Coltonton/Subaru-OpenPilot-Giraffe/Pictures/image0.jpg

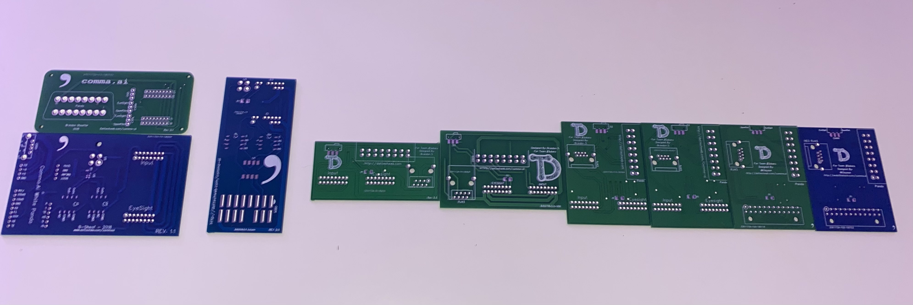
Pictures/image0.jpg
