Coltonton/Subaru-OpenPilot-Giraffe/Pictures/V3/3.1-Viki(1).JPG

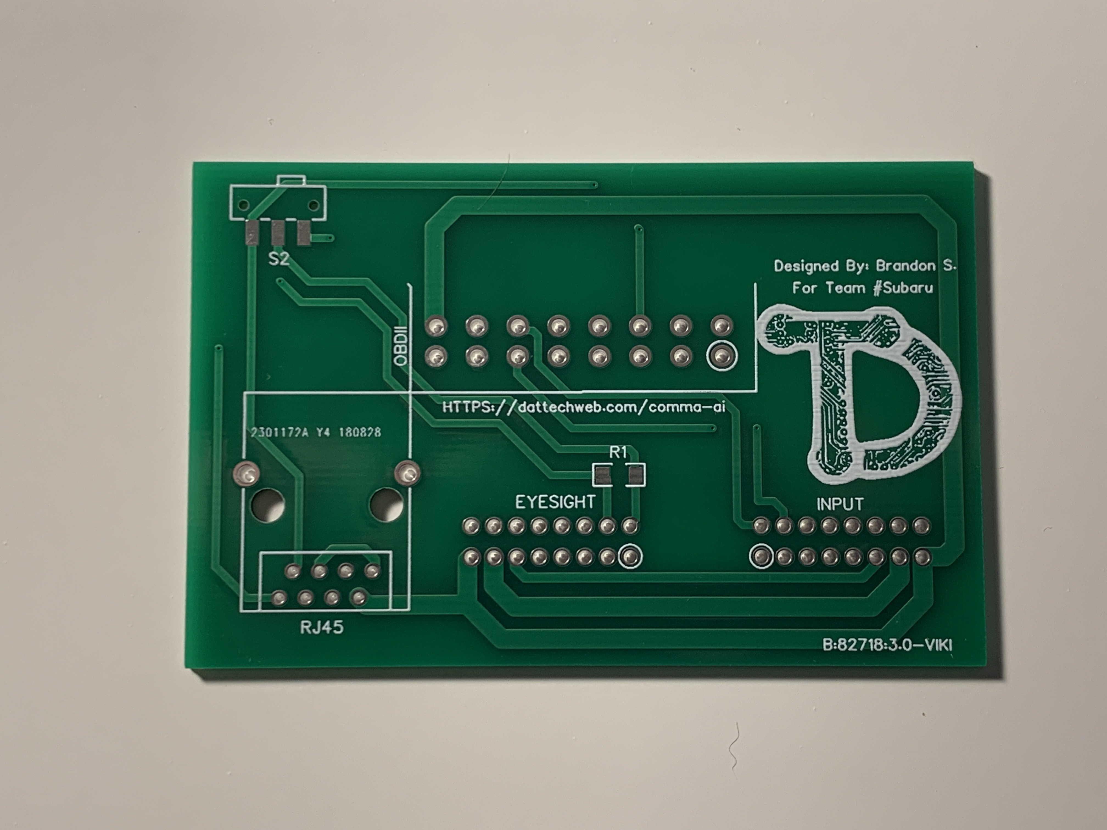
Pictures/V3/3.1-Viki(1).JPG
