Coltonton/Subaru-OpenPilot-Giraffe/Pictures/V3/3.6-Linda(2).jpg

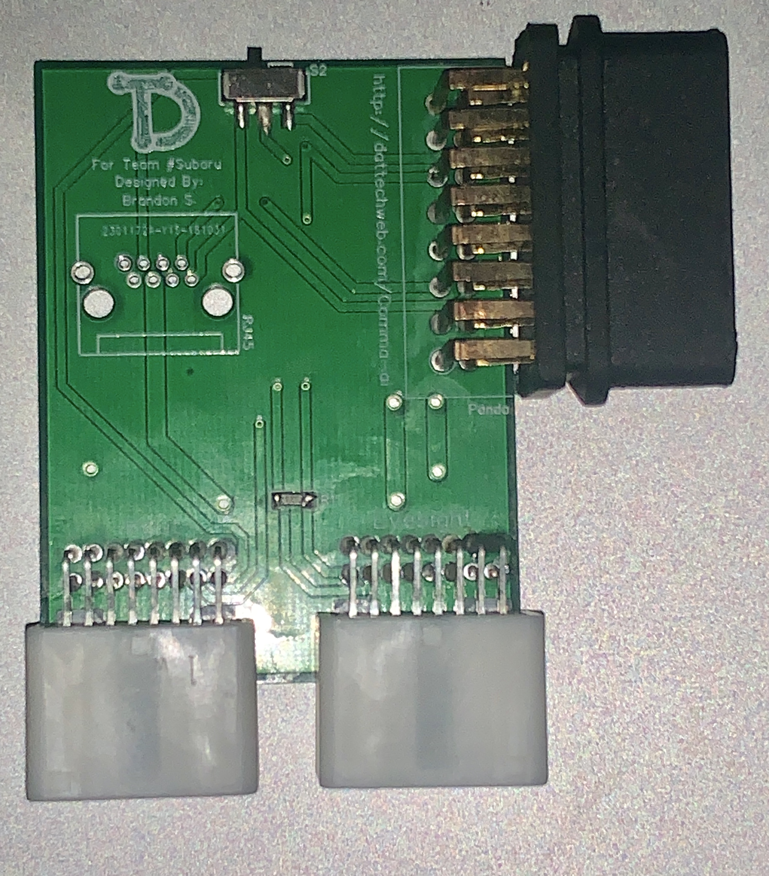
Pictures/V3/3.6-Linda(2).jpg
