Coltonton/Subaru-OpenPilot-Giraffe/Pictures/V3/3.7 - 3.8 Insallation Example.jpg

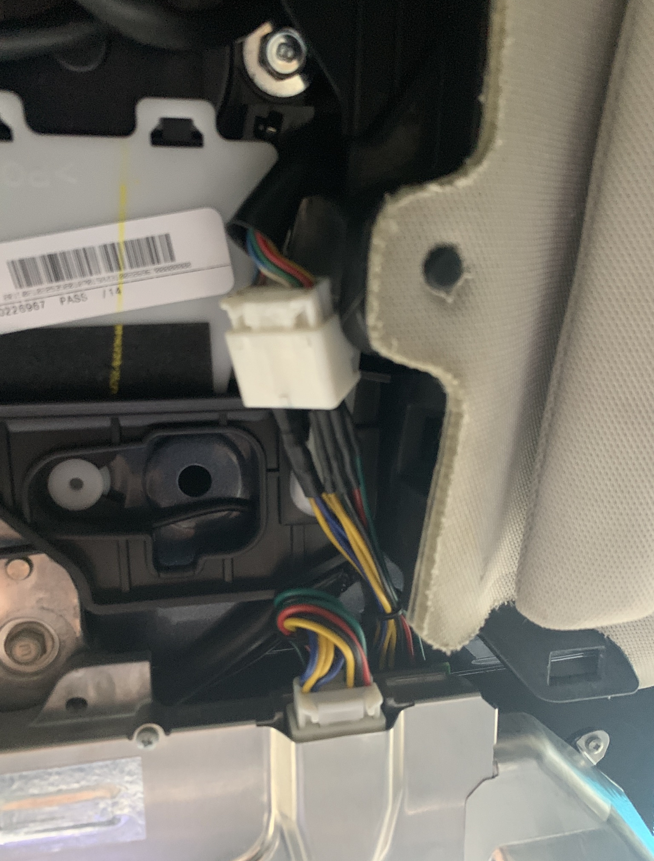
Pictures/V3/3.7 - 3.8 Insallation Example.jpg
