Coltonton/Subaru-OpenPilot-Giraffe/Pictures/V3/3.7-Cynthia(1).jpg

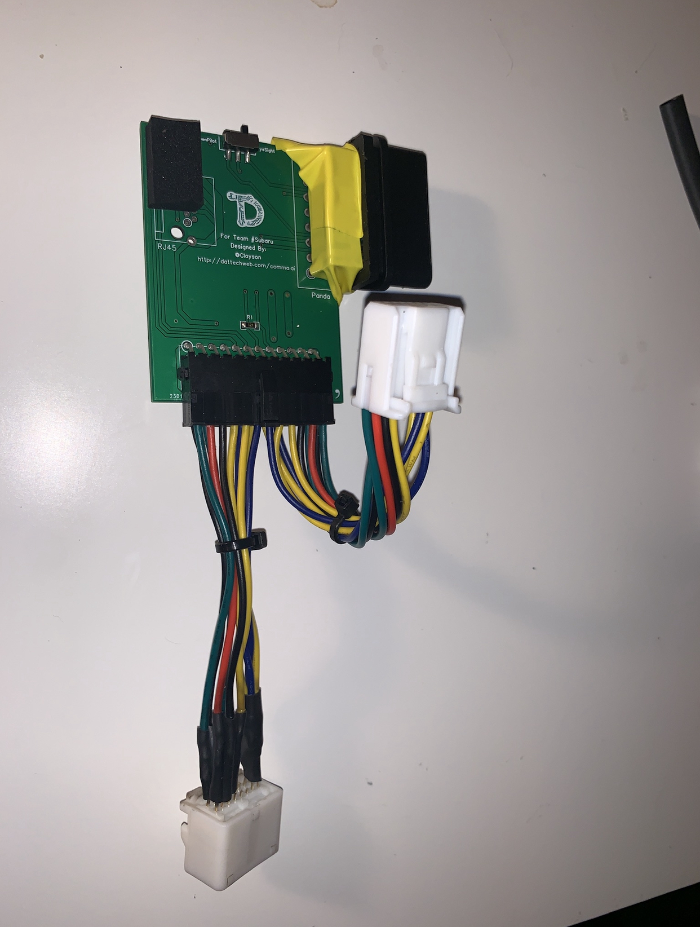
Pictures/V3/3.7-Cynthia(1).jpg
