Coltonton/Subaru-OpenPilot-Giraffe/Pictures/V3/3.7-Cynthia(2).JPG

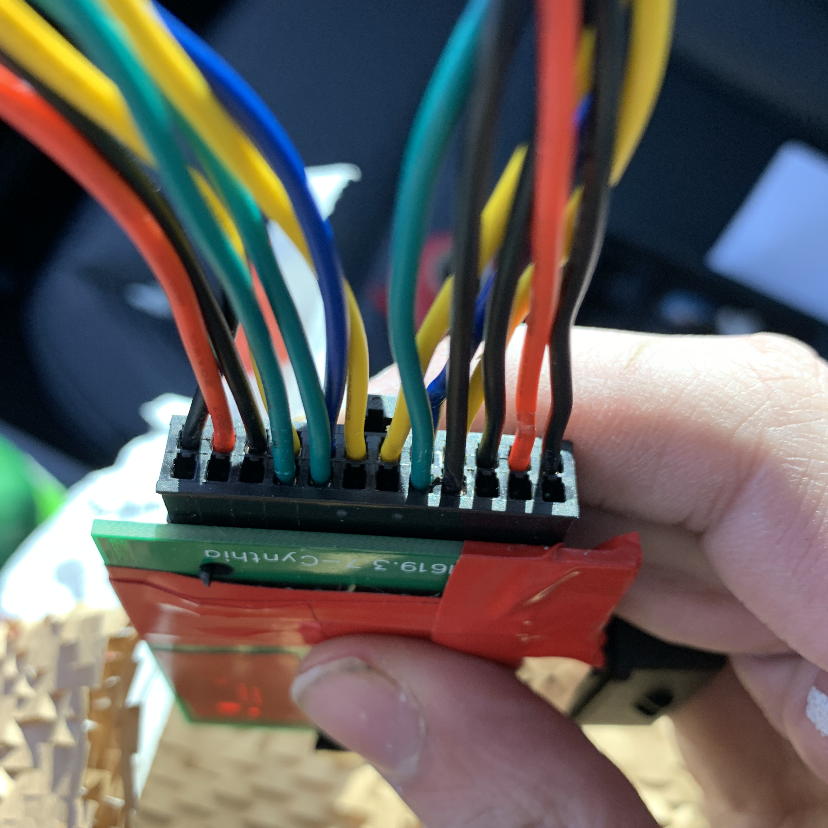
Pictures/V3/3.7-Cynthia(2).JPG
