Coltonton/Subaru-OpenPilot-Giraffe/Pictures/V3/3.7-Cynthia(6).JPG

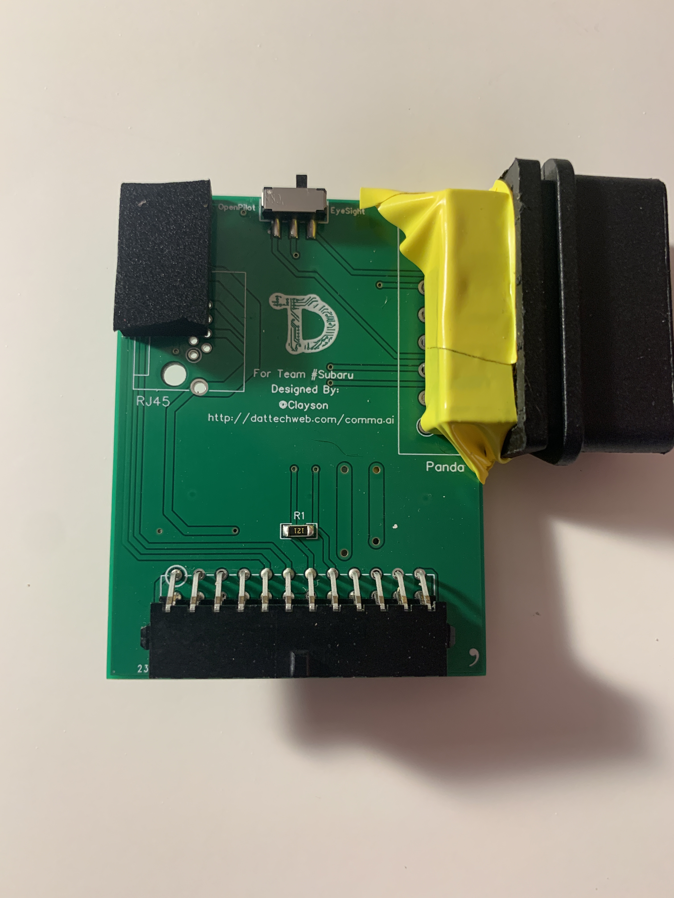
Pictures/V3/3.7-Cynthia(6).JPG
