Coltonton/Subaru-OpenPilot-Giraffe/Pictures/V3/3.8-Austin(2).JPG

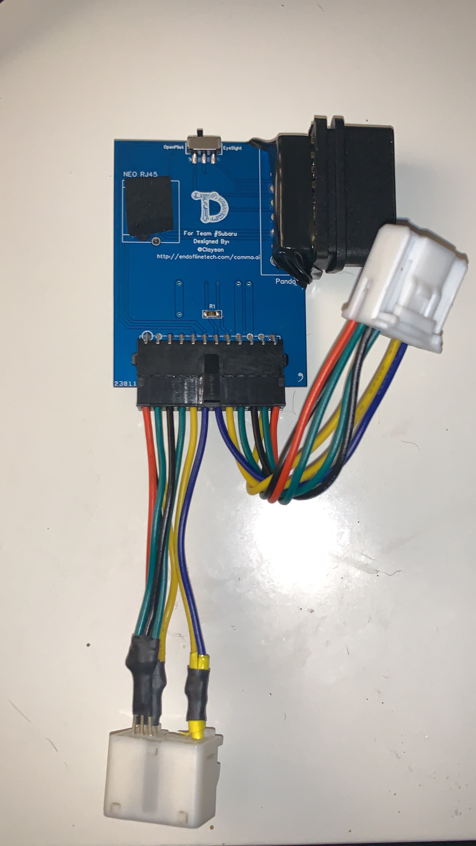
Pictures/V3/3.8-Austin(2).JPG
