Coltonton/Subaru-OpenPilot-Giraffe/Pictures/V3/3.8-Austin(4).jpg

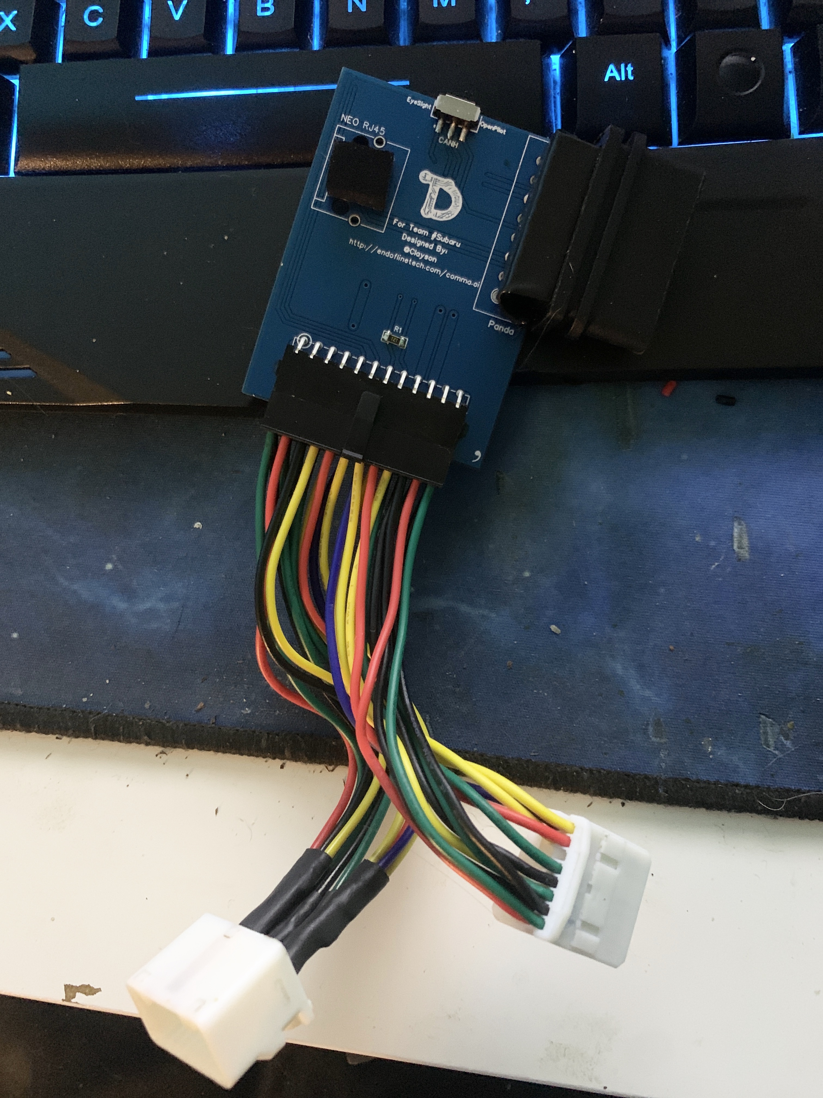
Pictures/V3/3.8-Austin(4).jpg
