Coltonton/Subaru-OpenPilot-Giraffe/Pictures/V3/(2).JPG

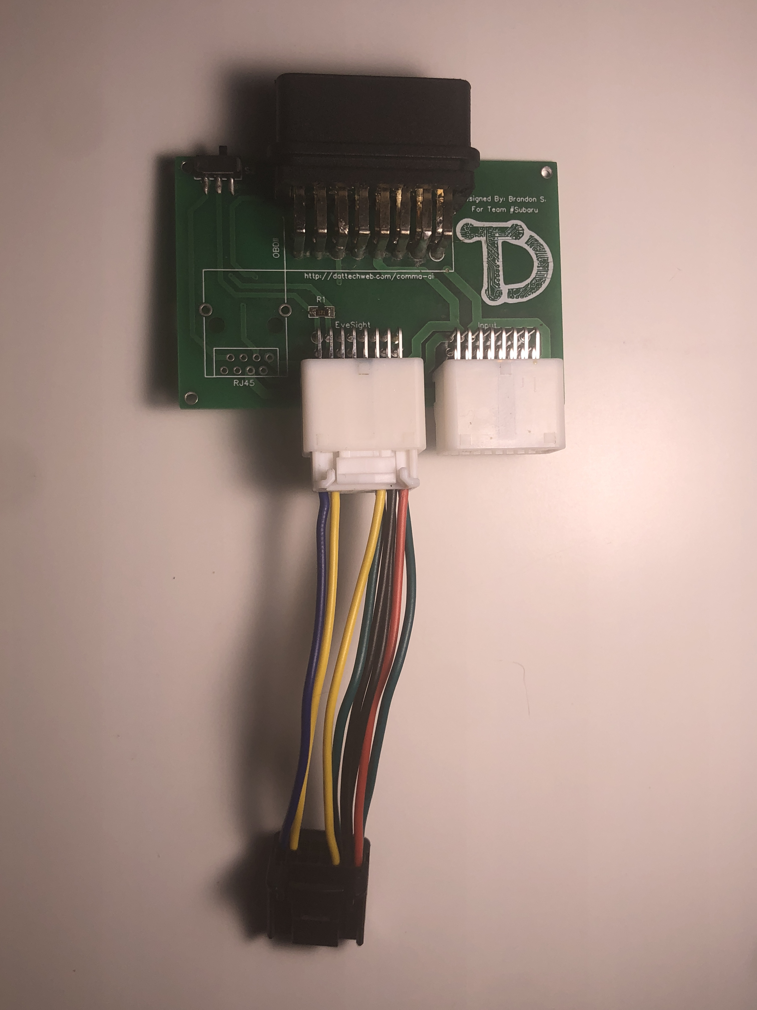
Pictures/V3/(2).JPG
