Coltonton/Subaru-OpenPilot-Giraffe/Pictures/V3/Comparison.JPG

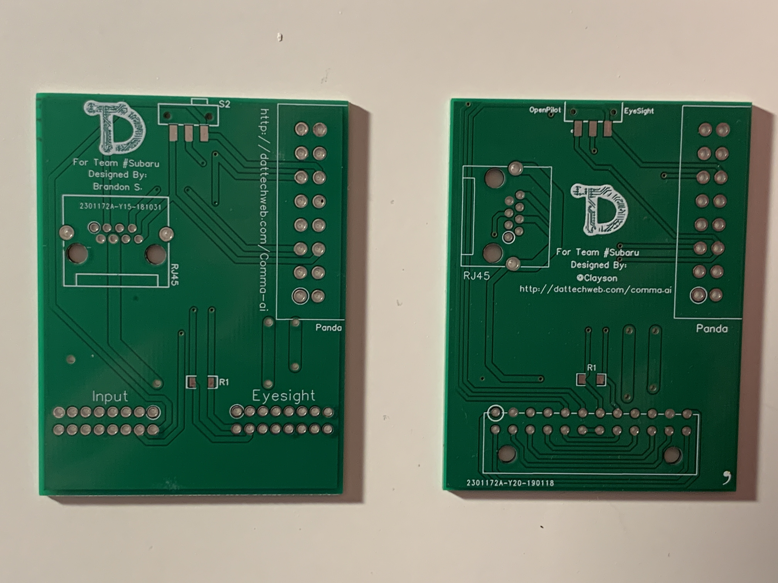
Pictures/V3/Comparison.JPG
