Coltonton/Subaru-OpenPilot-Giraffe/V3.8.3-Austin/0. Photos/brd.png

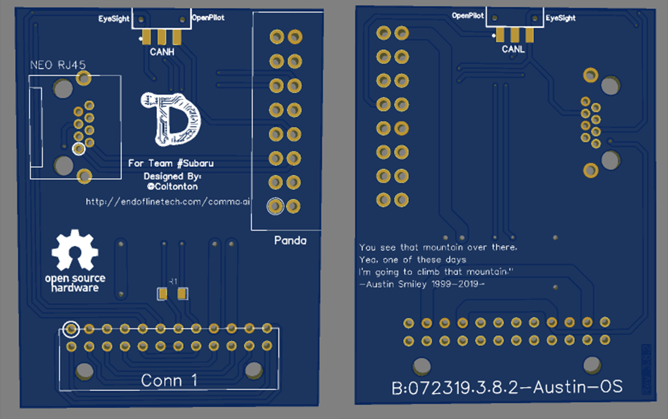
V3.8.3-Austin/0. Photos/brd.png
