Coltonton/Subaru-OpenPilot-Giraffe/V3.8.3-Austin/0. Photos/track.png

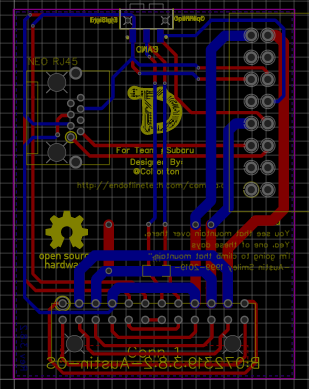
V3.8.3-Austin/0. Photos/track.png
