Coltonton/Subaru-OpenPilot-Giraffe/Pictures/V3/Installation Example(2).jpg

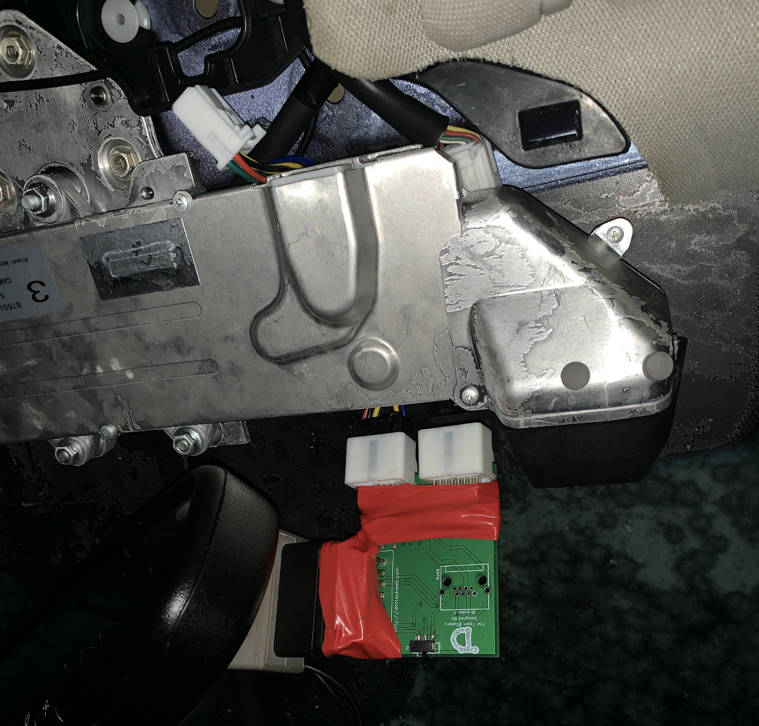
Pictures/V3/Installation Example(2).jpg
