Coltonton/Subaru-OpenPilot-Giraffe/Pictures/V3/3.4-Niki(1).JPG

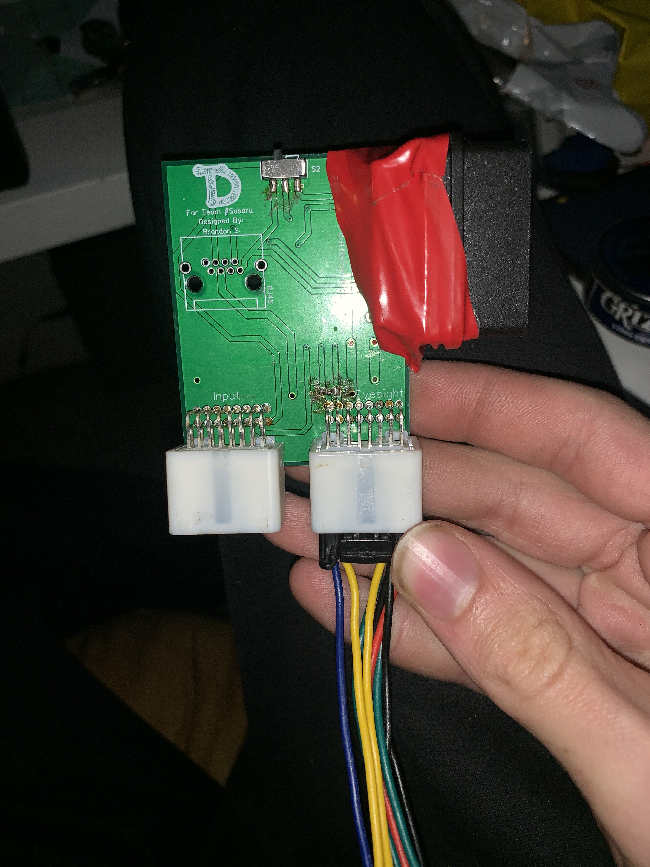
Pictures/V3/3.4-Niki(1).JPG
